2ndStar/Mia60XT/PCB/Mia60XT/Faen65XT.kicad_sch

## KiCad design PCB/Mia60XT/Faen65XT.kicad_sch (2022-11-03)

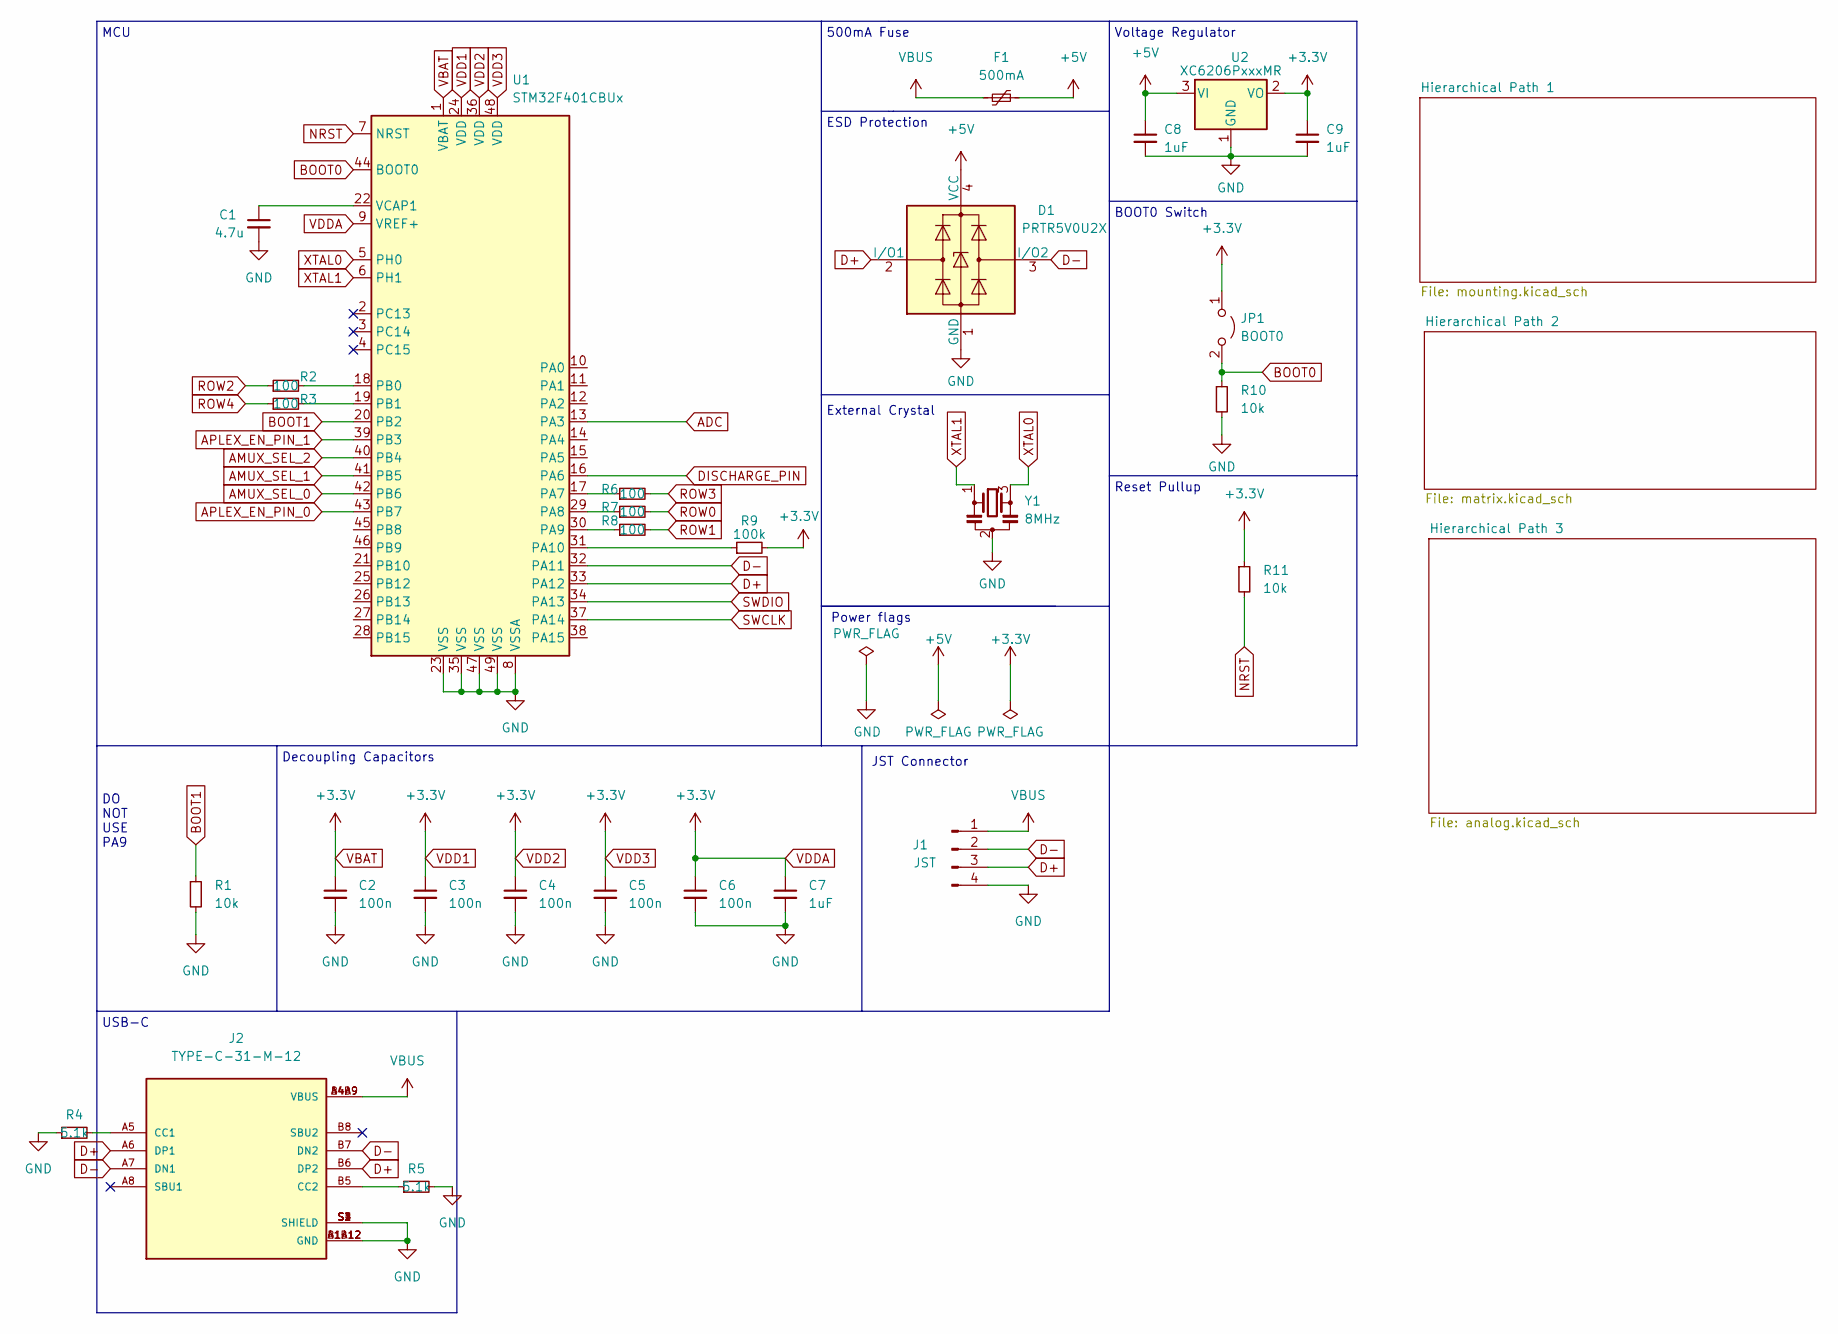
[picture p10: schematic Faen65XT.kicad_sch]

Parts:
C1: 4.7u; C_0402_1005Metric
C2, C3, C4, C5, C6: 100n; C_0402_1005Metric
C7, C8, C9: 1uF; C_0402_1005Metric
D1: PRTR5V0U2X; SOT-143
F1: 500mA; Fuse_1206_3216Metric
J1: JST; JST-SR-4
J2: TYPE-C-31-M-12; HRO_TYPE-C-31-M-12; PARTREV A
JP1: BOOT0; PinHeader_1x02_P2.54mm_Vertical
R1, R10, R11: 10k; R_0402_1005Metric
R2, R3, R6, R7, R8: 100; R_0402_1005Metric
R4, R5: 5.1k; R_0402_1005Metric
R9: 100k; R_0402_1005Metric
U1: STM32F401CBUx; QFN-48-1EP_7x7mm_P0.5mm_EP5.6x5.6mm
U2: XC6206PxxxMR; SOT-23
Y1: 8MHz; Resonator_SMD_Murata_CSTxExxV-3Pin_3.0x1.1mm

Connections:
+3.3V: C2.1, C3.1, C4.1, C5.1, C6.1, C7.1, C9.1, JP1.1 (A), R9.2, R11.1, U1.1 (VBAT), U1.9 (VREF+), U1.24 (VDD), U1.36 (VDD), U1.48 (VDD), U2.2 (VO)
+5V: C8.1, D1.4 (VCC), F1.2, U2.3 (VI)
ADC: U1.13 (PA3)
AMUX_SEL_0: U1.42 (PB6)
AMUX_SEL_1: U1.41 (PB5)
AMUX_SEL_2: U1.40 (PB4)
APLEX_EN_PIN_0: U1.43 (PB7)
APLEX_EN_PIN_1: U1.39 (PB3)
BOOT0: JP1.2 (B), R10.1, U1.44 (BOOT0)
BOOT1: R1.1, U1.20 (PB2)
D+: D1.2 (I/O1), J1.3, J2.A6 (DP1), J2.B6 (DP2), U1.33 (PA12)
D-: D1.3 (I/O2), J1.2, J2.A7 (DN1), J2.B7 (DN2), U1.32 (PA11)
DISCHARGE_PIN: U1.16 (PA6)
GND: C1.2, C2.2, C3.2, C4.2, C5.2, C6.2, C7.2, C8.2, C9.2, D1.1 (GND), J1.4, J2.A1B12 (GND), J2.B1A12 (GND), J2.S1 (SHIELD), J2.S2 (SHIELD), J2.S3 (SHIELD), J2.S4 (SHIELD), R1.2, R4.1, R5.2, R10.2, U1.8 (VSSA), U1.23 (VSS), U1.35 (VSS), U1.47 (VSS), U1.49 (VSS), U2.1 (GND), Y1.2
NRST: R11.2, U1.7 (NRST)
unnamed: C1.1, U1.22 (VCAP1)
unnamed: J2.A5 (CC1), R4.2
unnamed: J2.B5 (CC2), R5.1
unnamed: R2.2, U1.18 (PB0)
unnamed: R3.2, U1.19 (PB1)
unnamed: R6.1, U1.17 (PA7)
unnamed: R7.1, U1.29 (PA8)
unnamed: R8.1, U1.30 (PA9)
unnamed: R9.1, U1.31 (PA10)
ROW0: R7.2
ROW1: R8.2
ROW2: R2.1
ROW3: R6.2
ROW4: R3.1
SWCLK: U1.37 (PA14)
SWDIO: U1.34 (PA13)
VBUS: F1.1, J1.1, J2.A4B9 (VBUS), J2.B4A9 (VBUS)
XTAL0: U1.5 (PH0), Y1.3
XTAL1: U1.6 (PH1), Y1.1

Notes on the sheet:
Decoupling Capacitors
JST Connector
Voltage Regulator
USB-C
ESD Protection
MCU
BOOT0 Switch
Power flags
External Crystal
Reset Pullup
DO NOT USE PA9
500mA Fuse
