2ndStar/Mia60XT/PCB/Mia60XT/analog.kicad_sch

## KiCad design PCB/Mia60XT/analog.kicad_sch (2022-11-03)

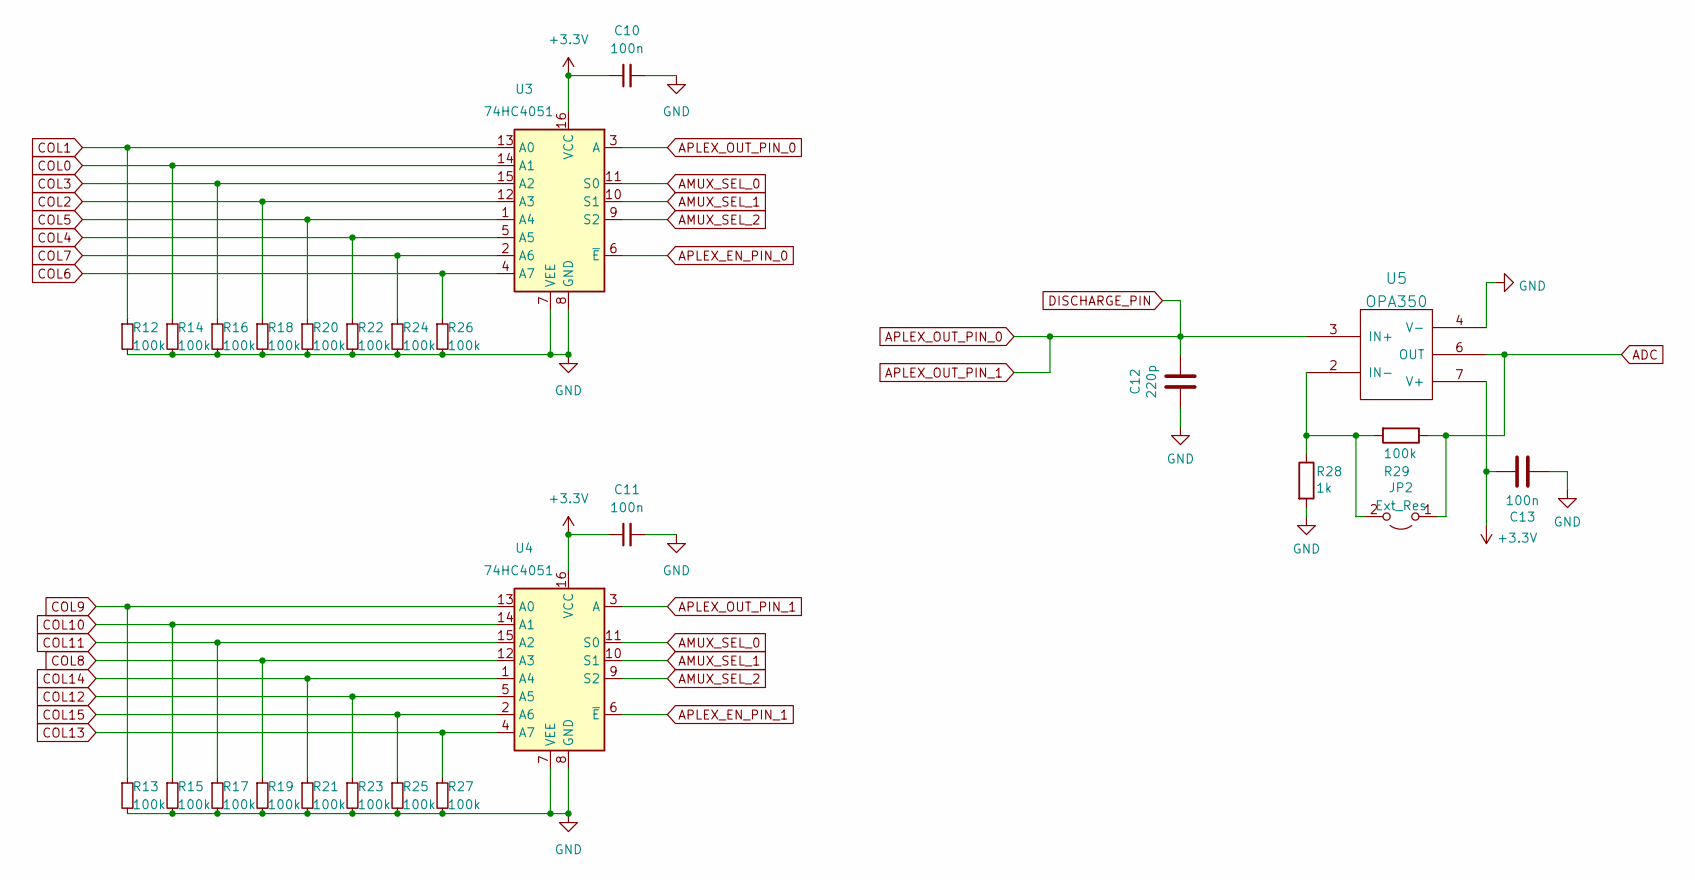
[picture p11: schematic analog.kicad_sch]

Parts:
C10, C11: 100n; C_0402_1005Metric
C12: 220p; C_0402_1005Metric; LCSC C1530
C13: 100n; C_0402_1005Metric; LCSC C307331
JP2: Ext_Res; R_0603_1608Metric_Pad0.98x0.95mm_HandSolder
R12, R13, R14, R15, R16, R17, R18, R19, R20, R21, R22, R23, R24, R25, R26, R27: 100k; R_0402_1005Metric
R28: 1k; R_0402_1005Metric; LCSC C11702
R29: 100k; R_0402_1005Metric; LCSC C25741
U3, U4: 74HC4051; TSSOP16
U5: OPA350; SOIC-8_3.9x4.9mm_P1.27mm; LCSC C13388

Connections:
+3.3V: C10.1, C11.1, C13.2, U3.16 (VCC), U4.16 (VCC), U5.7 (V+)
ADC: JP2.1 (A), R29.1, U5.6 (OUT)
AMUX_SEL_0: U3.11 (S0), U4.11 (S0)
AMUX_SEL_1: U3.10 (S1), U4.10 (S1)
AMUX_SEL_2: U3.9 (S2), U4.9 (S2)
APLEX_EN_PIN_0: U3.6 (~E)
APLEX_EN_PIN_1: U4.6 (~E)
APLEX_OUT_PIN_0: C12.1, U3.3 (A), U4.3 (A), U5.3 (IN+)
COL0: R14.1, U3.14 (A1)
COL1: R12.1, U3.13 (A0)
COL2: R18.1, U3.12 (A3)
COL3: R16.1, U3.15 (A2)
COL4: R22.1, U3.5 (A5)
COL5: R20.1, U3.1 (A4)
COL6: R26.1, U3.4 (A7)
COL7: R24.1, U3.2 (A6)
COL8: R19.1, U4.12 (A3)
COL9: R13.1, U4.13 (A0)
COL10: R15.1, U4.14 (A1)
COL11: R17.1, U4.15 (A2)
COL12: R23.1, U4.5 (A5)
COL13: R27.1, U4.4 (A7)
COL14: R21.1, U4.1 (A4)
COL15: R25.1, U4.2 (A6)
GND: C10.2, C11.2, C12.2, C13.1, R12.2, R13.2, R14.2, R15.2, R16.2, R17.2, R18.2, R19.2, R20.2, R21.2, R22.2, R23.2, R24.2, R25.2, R26.2, R27.2, R28.2, U3.7 (VEE), U3.8 (GND), U4.7 (VEE), U4.8 (GND), U5.4 (V-)
unnamed: JP2.2 (B), R28.1, R29.2, U5.2 (IN-)
