2ndStar/Mia60XT/PCB/Mia60XT/matrix.kicad_sch

## KiCad design PCB/Mia60XT/matrix.kicad_sch (2022-11-03)

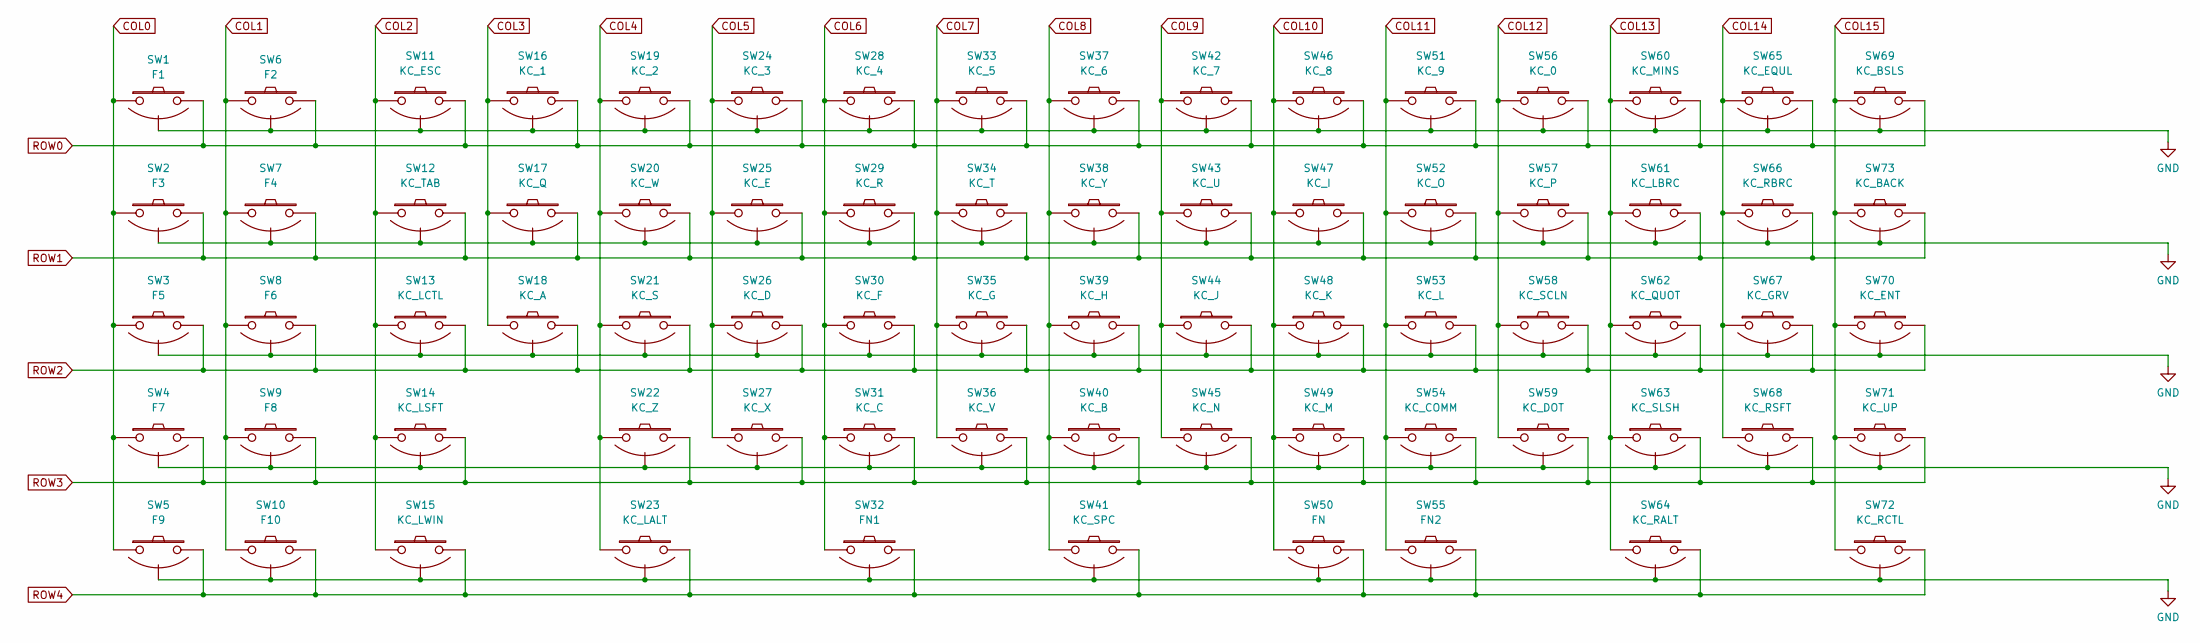
[picture p12: schematic matrix.kicad_sch]

Parts:
SW1: F1; ecs_pad_no_ring
SW2: F3; ecs_pad_no_ring
SW3: F5; ecs_pad_no_ring
SW4: F7; ecs_pad_no_ring
SW5: F9; ecs_pad_no_ring
SW6: F2; ecs_pad_no_ring
SW7: F4; ecs_pad_no_ring
SW8: F6; ecs_pad_no_ring
SW9: F8; ecs_pad_no_ring
SW10: F10; ecs_pad_no_ring
SW11: KC_ESC; ecs_pad_no_ring
SW12: KC_TAB; ecs_pad_no_ring
SW13: KC_LCTL; ecs_pad_no_ring
SW14: KC_LSFT; ecs_pad_no_ring
SW15: KC_LWIN; ecs_pad_no_ring
SW16: KC_1; ecs_pad_no_ring
SW17: KC_Q; ecs_pad_no_ring
SW18: KC_A; ecs_pad_no_ring
SW19: KC_2; ecs_pad_no_ring
SW20: KC_W; ecs_pad_no_ring
SW21: KC_S; ecs_pad_no_ring
SW22: KC_Z; ecs_pad_no_ring
SW23: KC_LALT; ecs_pad_no_ring
SW24: KC_3; ecs_pad_no_ring
SW25: KC_E; ecs_pad_no_ring
SW26: KC_D; ecs_pad_no_ring
SW27: KC_X; ecs_pad_no_ring
SW28: KC_4; ecs_pad_no_ring
SW29: KC_R; ecs_pad_no_ring
SW30: KC_F; ecs_pad_no_ring
SW31: KC_C; ecs_pad_no_ring
SW32: FN1; ecs_pad_no_ring
SW33: KC_5; ecs_pad_no_ring
SW34: KC_T; ecs_pad_no_ring
SW35: KC_G; ecs_pad_no_ring
SW36: KC_V; ecs_pad_no_ring
SW37: KC_6; ecs_pad_no_ring
SW38: KC_Y; ecs_pad_no_ring
SW39: KC_H; ecs_pad_no_ring
SW40: KC_B; ecs_pad_no_ring
SW41: KC_SPC; ecs_pad_no_ring
SW42: KC_7; ecs_pad_no_ring
SW43: KC_U; ecs_pad_no_ring
SW44: KC_J; ecs_pad_no_ring
SW45: KC_N; ecs_pad_no_ring
SW46: KC_8; ecs_pad_no_ring
SW47: KC_I; ecs_pad_no_ring
SW48: KC_K; ecs_pad_no_ring
SW49: KC_M; ecs_pad_no_ring
SW50: FN; ecs_pad_no_ring
SW51: KC_9; ecs_pad_no_ring
SW52: KC_O; ecs_pad_no_ring
SW53: KC_L; ecs_pad_no_ring
SW54: KC_COMM; ecs_pad_no_ring
SW55: FN2; ecs_pad_no_ring
SW56: KC_0; ecs_pad_no_ring
SW57: KC_P; ecs_pad_no_ring
SW58: KC_SCLN; ecs_pad_no_ring
SW59: KC_DOT; ecs_pad_no_ring
SW60: KC_MINS; ecs_pad_no_ring
SW61: KC_LBRC; ecs_pad_no_ring
SW62: KC_QUOT; ecs_pad_no_ring
SW63: KC_SLSH; ecs_pad_no_ring
SW64: KC_RALT; ecs_pad_no_ring
SW65: KC_EQUL; ecs_pad_no_ring
SW66: KC_RBRC; ecs_pad_no_ring
SW67: KC_GRV; ecs_pad_no_ring
SW68: KC_RSFT; ecs_pad_no_ring
SW69: KC_BSLS; ecs_pad_no_ring
SW70: KC_ENT; ecs_pad_no_ring
SW71: KC_UP; ecs_pad_no_ring
SW72: KC_RCTL; ecs_pad_no_ring
SW73: KC_BACK; ecs_pad_no_ring

Connections:
COL0: SW1.1, SW2.1, SW3.1, SW4.1, SW5.1
COL1: SW6.1, SW7.1, SW8.1, SW9.1, SW10.1
COL2: SW11.1, SW12.1, SW13.1, SW14.1, SW15.1
COL3: SW16.1, SW17.1, SW18.1
COL4: SW19.1, SW20.1, SW21.1, SW22.1, SW23.1
COL5: SW24.1, SW25.1, SW26.1, SW27.1
COL6: SW28.1, SW29.1, SW30.1, SW31.1, SW32.1
COL7: SW33.1, SW34.1, SW35.1, SW36.1
COL8: SW37.1, SW38.1, SW39.1, SW40.1, SW41.1
COL9: SW42.1, SW43.1, SW44.1, SW45.1
COL10: SW46.1, SW47.1, SW48.1, SW49.1, SW50.1
COL11: SW51.1, SW52.1, SW53.1, SW54.1, SW55.1
COL12: SW56.1, SW57.1, SW58.1, SW59.1
COL13: SW60.1, SW61.1, SW62.1, SW63.1, SW64.1
COL14: SW65.1, SW66.1, SW67.1, SW68.1
COL15: SW69.1, SW70.1, SW71.1, SW72.1, SW73.1
GND: SW1.3 (SG), SW2.3 (SG), SW3.3 (SG), SW4.3 (SG), SW5.3 (SG), SW6.3 (SG), SW7.3 (SG), SW8.3 (SG), SW9.3 (SG), SW10.3 (SG), SW11.3 (SG), SW12.3 (SG), SW13.3 (SG), SW14.3 (SG), SW15.3 (SG), SW16.3 (SG), SW17.3 (SG), SW18.3 (SG), SW19.3 (SG), SW20.3 (SG), SW21.3 (SG), SW22.3 (SG), SW23.3 (SG), SW24.3 (SG), SW25.3 (SG), SW26.3 (SG), SW27.3 (SG), SW28.3 (SG), SW29.3 (SG), SW30.3 (SG), SW31.3 (SG), SW32.3 (SG), SW33.3 (SG), SW34.3 (SG), SW35.3 (SG), SW36.3 (SG), SW37.3 (SG), SW38.3 (SG), SW39.3 (SG), SW40.3 (SG), SW41.3 (SG), SW42.3 (SG), SW43.3 (SG), SW44.3 (SG), SW45.3 (SG), SW46.3 (SG), SW47.3 (SG), SW48.3 (SG), SW49.3 (SG), SW50.3 (SG), SW51.3 (SG), SW52.3 (SG), SW53.3 (SG), SW54.3 (SG), SW55.3 (SG), SW56.3 (SG), SW57.3 (SG), SW58.3 (SG), SW59.3 (SG), SW60.3 (SG), SW61.3 (SG), SW62.3 (SG), SW63.3 (SG), SW64.3 (SG), SW65.3 (SG), SW66.3 (SG), SW67.3 (SG), SW68.3 (SG), SW69.3 (SG), SW70.3 (SG), SW71.3 (SG), SW72.3 (SG), SW73.3 (SG)
ROW0: SW1.2, SW6.2, SW11.2, SW16.2, SW19.2, SW24.2, SW28.2, SW33.2, SW37.2, SW42.2, SW46.2, SW51.2, SW56.2, SW60.2, SW65.2, SW69.2
ROW1: SW2.2, SW7.2, SW12.2, SW17.2, SW20.2, SW25.2, SW29.2, SW34.2, SW38.2, SW43.2, SW47.2, SW52.2, SW57.2, SW61.2, SW66.2, SW73.2
ROW2: SW3.2, SW8.2, SW13.2, SW18.2, SW21.2, SW26.2, SW30.2, SW35.2, SW39.2, SW44.2, SW48.2, SW53.2, SW58.2, SW62.2, SW67.2, SW70.2
ROW3: SW4.2, SW9.2, SW14.2, SW22.2, SW27.2, SW31.2, SW36.2, SW40.2, SW45.2, SW49.2, SW54.2, SW59.2, SW63.2, SW68.2, SW71.2
ROW4: SW5.2, SW10.2, SW15.2, SW23.2, SW32.2, SW41.2, SW50.2, SW55.2, SW64.2, SW72.2
